disenoUDP/sinte-555/kicad/sinte555/sinte555.kicad_sch

## KiCad design kicad/sinte555/sinte555.kicad_sch (2026-08-27, an earlier design)

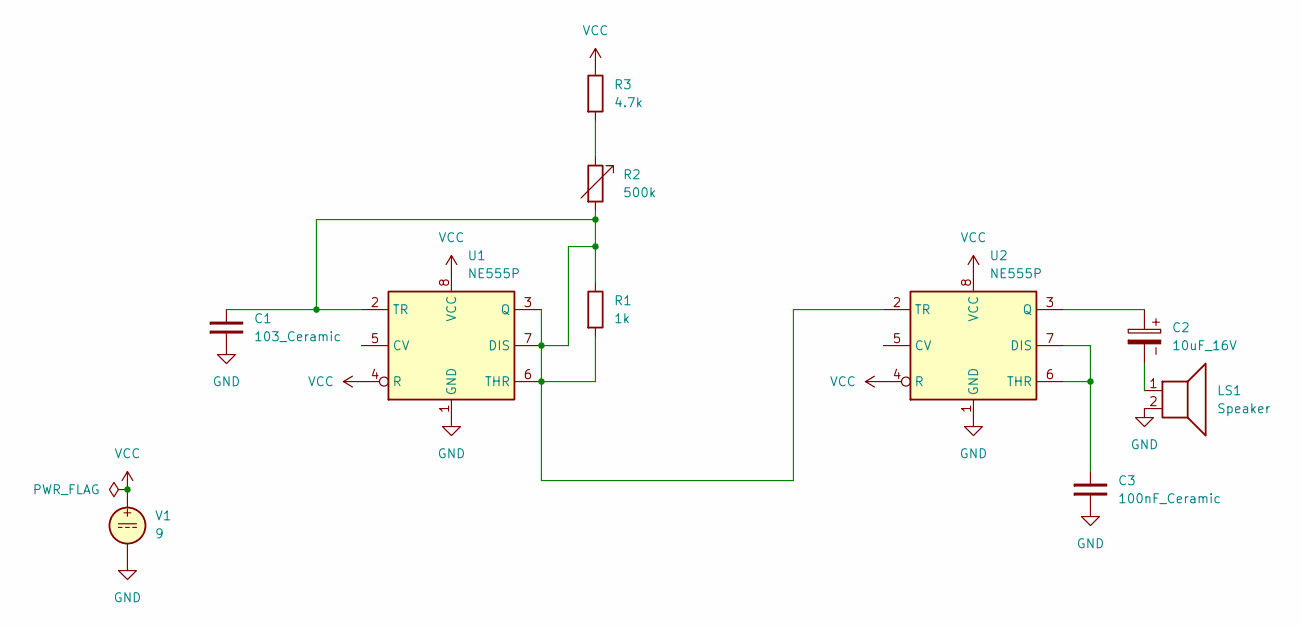
[picture p5: schematic sinte555.kicad_sch]

Parts:
C1: 103_Ceramic; C_Disc_D5.0mm_W2.5mm_P2.50mm
C2: 10uF_16V; CP_Radial_D5.0mm_P2.00mm
C3: 100nF_Ceramic; C_Disc_D5.0mm_W2.5mm_P2.50mm
LS1: Speaker
R1: 1k
R2: 500k
R3: 4.7k
U1, U2: NE555P; DIP-8_W7.62mm
V1: 9

Connections:
GND: C1.1, C3.1, LS1.2, U1.1 (GND), U2.1 (GND), V1.2
unnamed: C1.2, R1.1, R1.2, R2.2, U1.2 (TR), U1.3 (Q), U1.6 (THR), U1.7 (DIS), U2.2 (TR)
unnamed: C2.1, U2.3 (Q)
unnamed: C2.2, LS1.1
unnamed: C3.2, U2.6 (THR), U2.7 (DIS)
unnamed: R2.1, R3.2
VCC: R3.1, U1.4 (R), U1.8 (VCC), U2.4 (R), U2.8 (VCC), V1.1
